stanislavsurmylo/CambridgeIDP_group5/3d_models/box_assembly.SLDASM

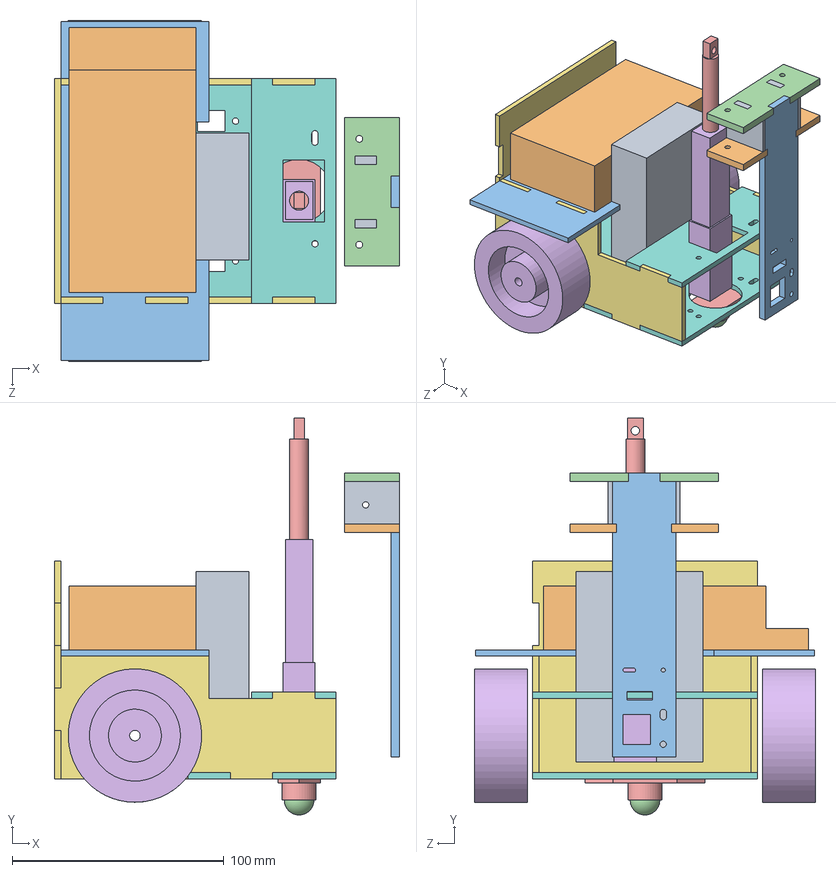
[picture p2: CAD file, 2025-11-24]
3d_models/box_assembly.SLDASM
162.9 x 187.4 x 161.0 mm
bottom
side x 2
wheel x 2
ballbearing mount
ballbearing
above_wheel
pico
battery
top
back
actuator_base
actuator_mover
forklift_baseplate
forklift_front_face
forklift_upper_notch x 2
forklift_vertical_edge x 2
