stanislavsurmylo/CambridgeIDP_group5/3d_models/ballbearing_and_mount.SLDASM

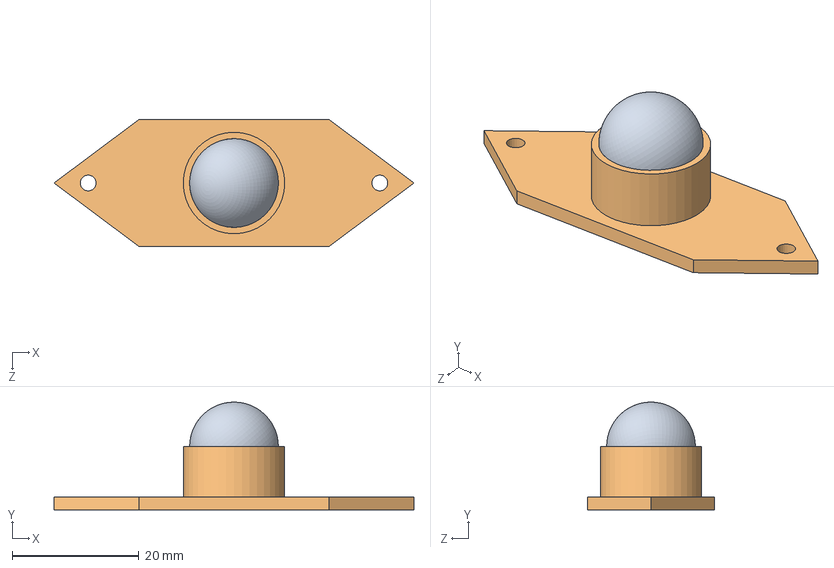
[picture p4: CAD file, 2025-11-17]
3d_models/ballbearing_and_mount.SLDASM
56.8 x 17.0 x 20.0 mm
ballbearing mount
ballbearing
