stanislavsurmylo/CambridgeIDP_group5/3d_models/laser cutting files/bottom.DXF

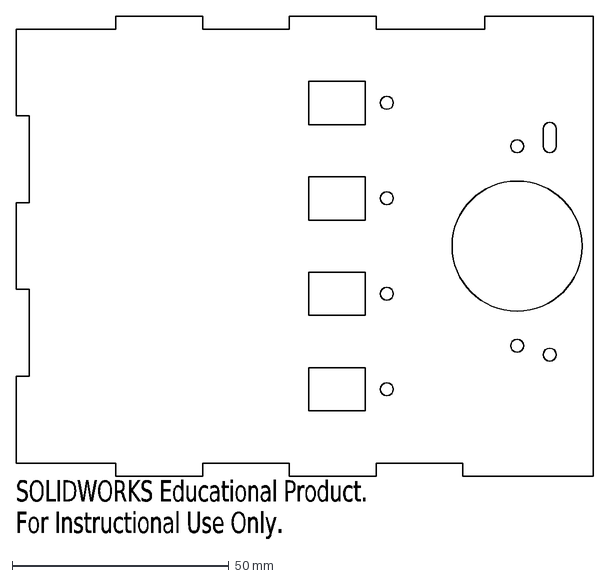
[picture p17: CAD file, 2025-11-24]
3d_models/laser cutting files/bottom.DXF
SOLIDWORKS Educational Product.
For Instructional Use Only.
