stanislavsurmylo/CambridgeIDP_group5/3d_models/back.SLDPRT

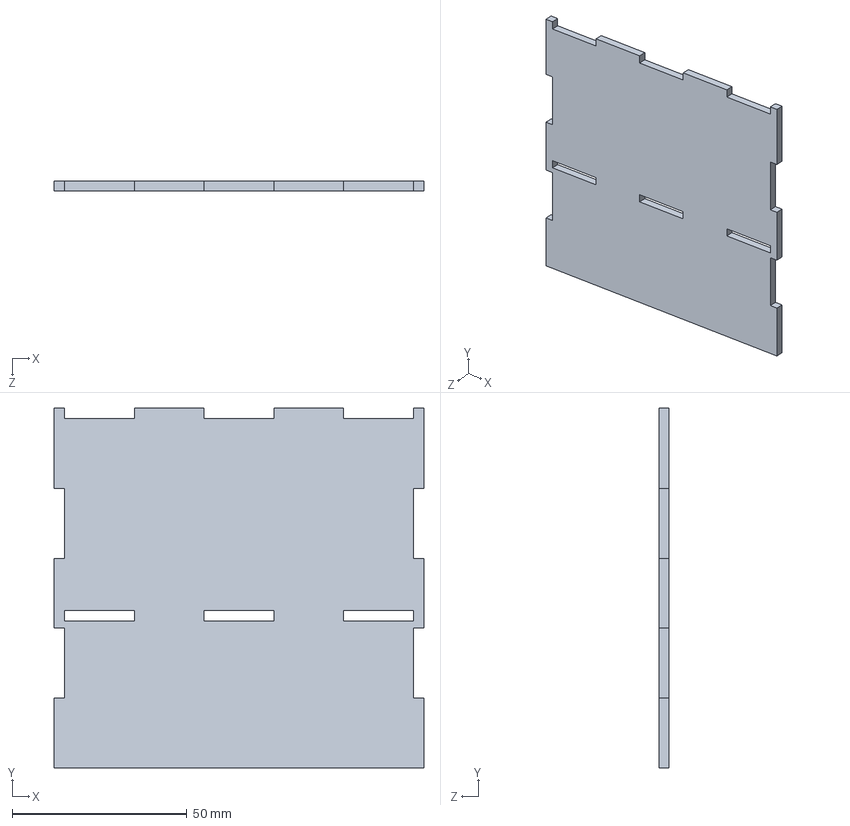
[picture p18: CAD file, 2025-11-24]
3d_models/back.SLDPRT
106.0 x 103.0 x 3.00 mm
