stanislavsurmylo/CambridgeIDP_group5/3d_models/pico.SLDPRT

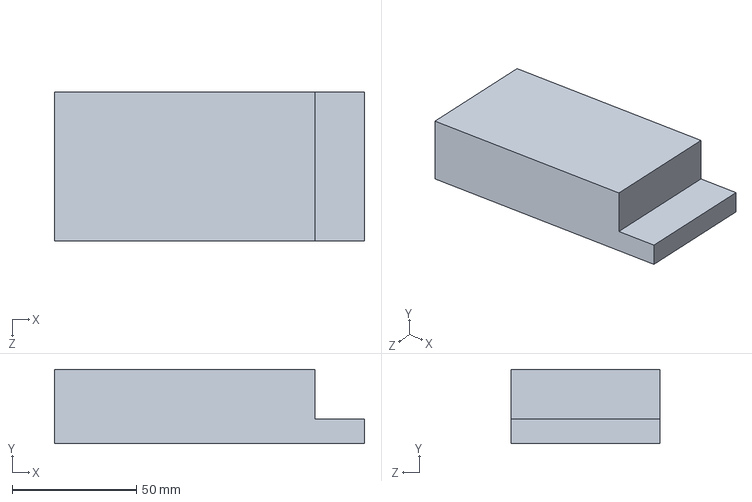
[picture p19: CAD file, 2025-11-17]
3d_models/pico.SLDPRT
125.0 x 30.0 x 60.0 mm
