stanislavsurmylo/CambridgeIDP_group5/3d_models/battery.SLDPRT

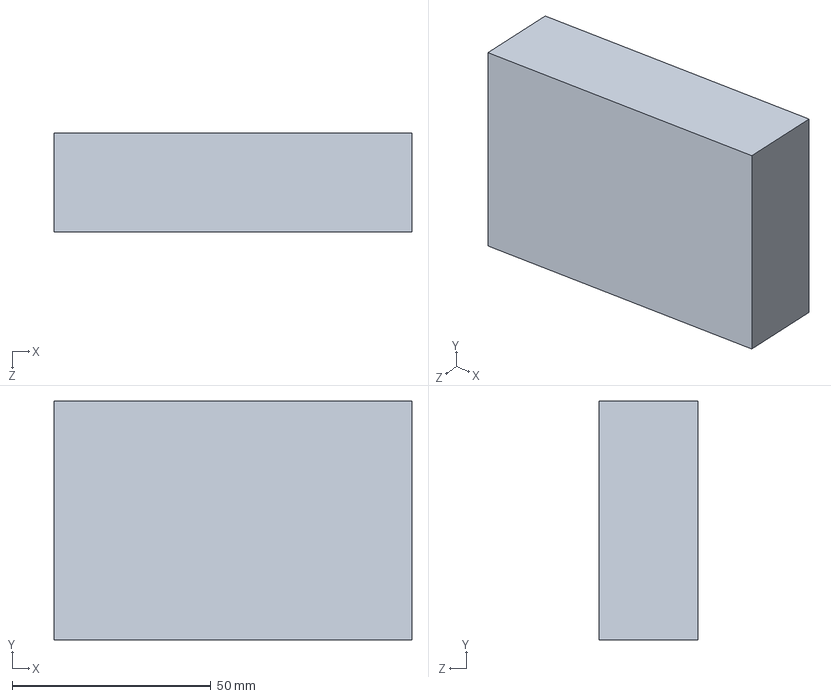
[picture p20: CAD file, 2025-11-17]
3d_models/battery.SLDPRT
90.0 x 60.0 x 25.0 mm
