stanislavsurmylo/CambridgeIDP_group5/3d_models/side.SLDPRT

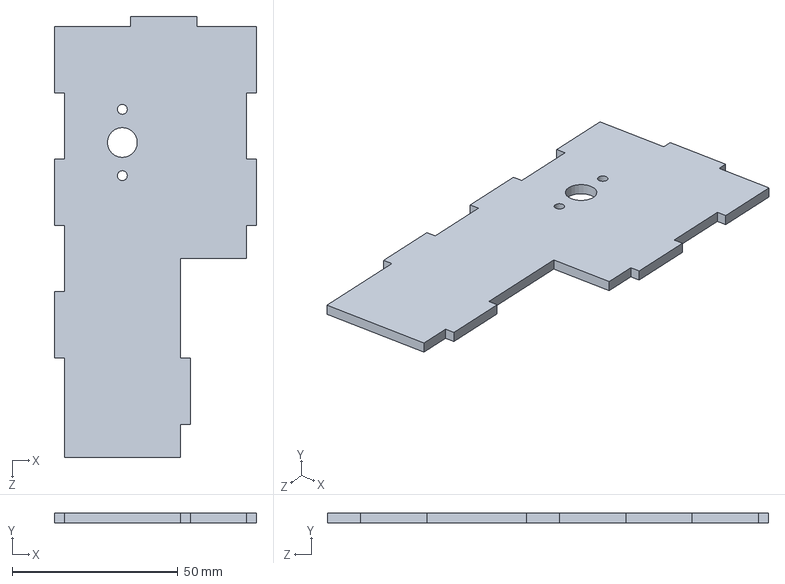
[picture p21: CAD file, 2025-11-17]
3d_models/side.SLDPRT
61.0 x 3.00 x 133.0 mm
