stanislavsurmylo/CambridgeIDP_group5/3d_models/above_wheel.SLDPRT

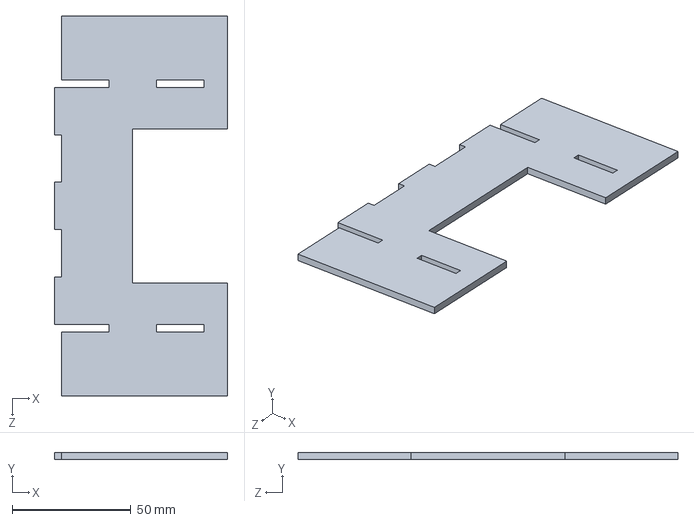
[picture p22: CAD file, 2025-11-17]
3d_models/above_wheel.SLDPRT
73.0 x 3.00 x 160.0 mm
