stanislavsurmylo/CambridgeIDP_group5/3d_models/ballbearing mount.SLDPRT

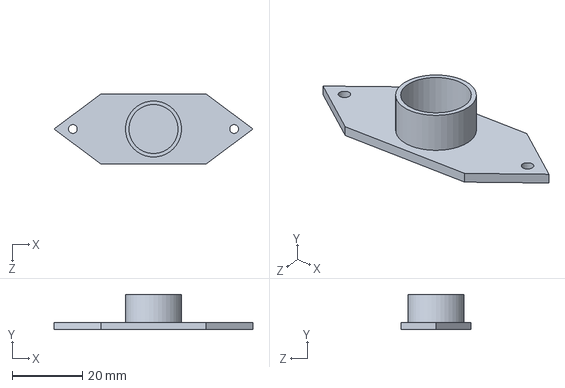
[picture p23: CAD file, 2025-11-17]
3d_models/ballbearing mount.SLDPRT
56.8 x 10.0 x 20.0 mm
