stanislavsurmylo/CambridgeIDP_group5/3d_models/ballbearing.SLDPRT

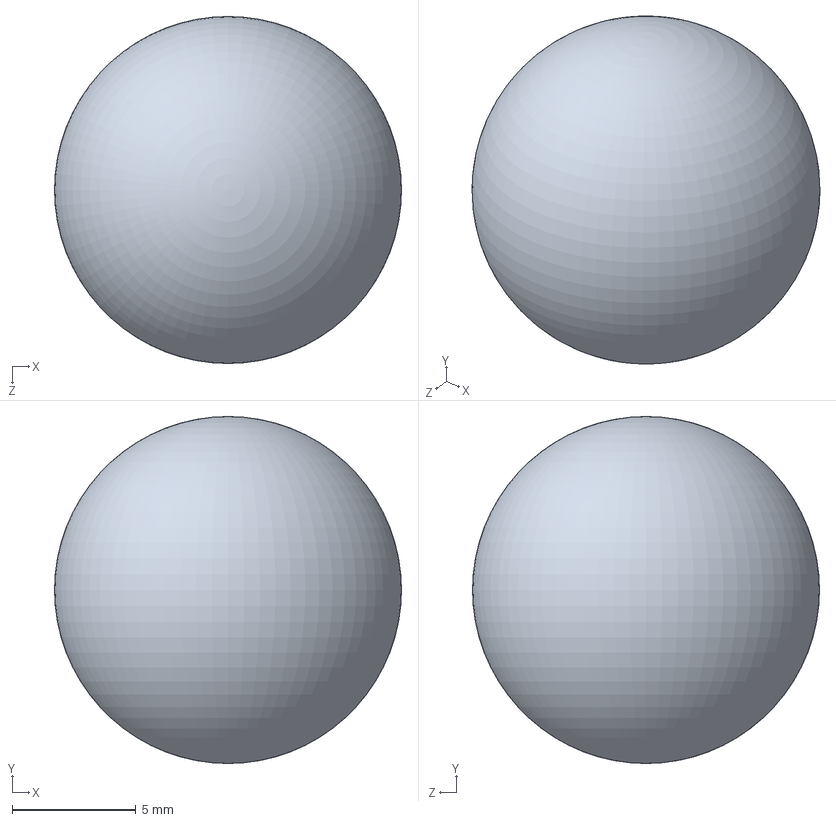
[picture p24: CAD file, 2025-11-17]
3d_models/ballbearing.SLDPRT
14.0 x 14.0 x 14.0 mm
