stanislavsurmylo/CambridgeIDP_group5/3d_models/wheel.SLDPRT

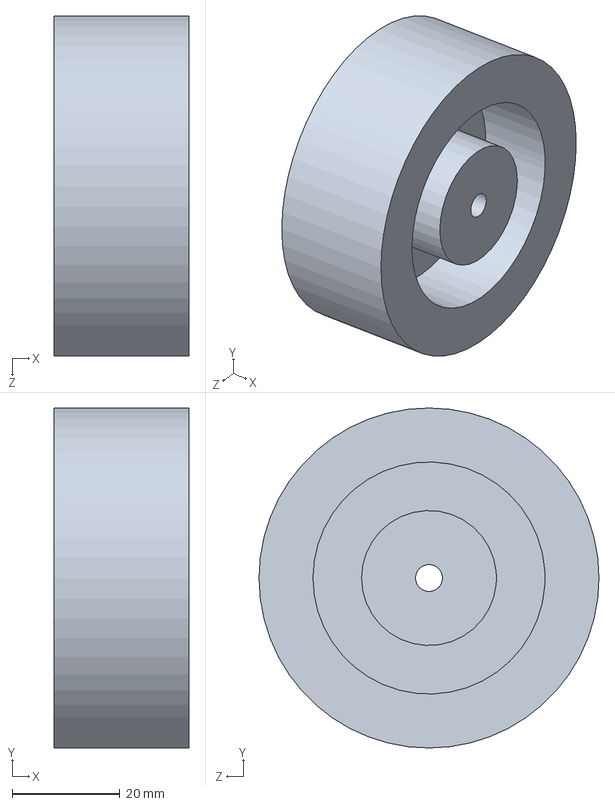
[picture p25: CAD file, 2025-11-17]
3d_models/wheel.SLDPRT
25.0 x 63.0 x 63.0 mm
