stanislavsurmylo/CambridgeIDP_group5/linear_actuator.py

from machine import Pin, PWM
from utime import sleep
# Lightweight helper around a brushed linear actuator using one PWM + one dir pin.

class Actuator:
    def __init__(self, dirPin, PWMPin):
        self.mDir = Pin(dirPin, Pin.OUT)  # set motor direction pin
        self.pwm = PWM(Pin(PWMPin))  # set motor pwm pin
        self.pwm.freq(1000)  # set PWM frequency
        self.pwm.duty_u16(0)  # set duty cycle - 0=off
           
    def set(self, dir, speed):
        self.mDir.value(dir)                     # forward = 0 reverse = 1 motor
        self.pwm.duty_u16(int(65535 * speed / 100))  # speed range 0-100 motor
    
    def stop(self):
        self.pwm.duty_u16(0)  # Stop the actuator
    
    def extend(self, speed=50):
        """Extend the actuator at specified speed (0-100)"""
        self.set(dir=0, speed=speed)
    
    def retract(self, speed=50):
        """Retract the actuator at specified speed (0-100)"""
        self.set(dir=1, speed=speed)

DIR_PIN = 3
PWM_PIN = 2

def unload_robot(actuator):
    # Full retract to offload weight before next lift cycle.
    DIR_PIN = 3
    PWM_PIN = 2
    TEST_DURATION = (50/50)*11  # 1 second for testing
    

    # Unloading robot to reduce weight on actuator
    
    # Test retract
    print("Retracting for {} seconds...".format(TEST_DURATION))
    actuator.retract(speed=50)
    sleep(TEST_DURATION)
    actuator.stop()
    print("Unloading complete")
    sleep(0.2)  # Pause so you can measure

def unload_robot_shift(actuator):
    # Short retract for repositioning after unloading.
    DIR_PIN = 3
    PWM_PIN = 2
    TEST_DURATION = (50/50)*4  # 1 second for testing
    

    # Unloading robot to reduce weight on actuator
    
    # Test retract
    print("Retracting for {} seconds...".format(TEST_DURATION))
    actuator.retract(speed=50)
    sleep(TEST_DURATION)
    actuator.stop()
    print("Unloading complete")
    sleep(0.2)  # Pause so you can measure


if __name__ == "__main__":
    unload_robot()
